kori-thespirit/LoraGatewayDevelopment/code/core/gateway/components/network/eth_w5500_app/include/eth_w5500_app.h

/* -------------------------- LICENSE placeholder -------------------------- */
#ifndef ETH_W5500_APP_H
#define ETH_W5500_APP_H
#include "network_event_group_define.h"
#include "freertos/FreeRTOS.h"
#include "freertos/task.h"
#include "freertos/event_groups.h"
void w5500_init(EventGroupHandle_t *net_eg);
#endif // ETH_W5500_APP_H
