kori-thespirit/LoraGatewayDevelopment/code/unit-test/unit-test_lora_node/components/lora/include/define.h

#ifndef DEFINE_H
#define DEFINE_H

#define CONFIG_CS_GPIO    21
#define CONFIG_MOSI_GPIO  19
#define CONFIG_MISO_GPIO  18
#define CONFIG_SCK_GPIO   4
#define CONFIG_RST_GPIO   22
#define HOST_ID           SPI2_HOST

#endif
