kori-thespirit/LoraGatewayDevelopment/code/unit-test/unit-test_lora_gateway/components/lora/include/define.h

#ifndef DEFINE_H
#define DEFINE_H

#define CONFIG_CS_GPIO    42
#define CONFIG_MOSI_GPIO  41
#define CONFIG_MISO_GPIO  40
#define CONFIG_SCK_GPIO   39
#define CONFIG_RST_GPIO   38
#define HOST_ID           SPI2_HOST

#endif
