kori-thespirit/LoraGatewayDevelopment/code/unit-test/unit-test_w5500_mqtt/main/main.c

#include "esp_err.h"
#include "ethernet_w5500.h"
#include "freertos/FreeRTOS.h"
#include "freertos/queue.h"
#include "freertos/task.h"
#include <stdint.h>

void app_main(void) {
  w5500_init();
  /* Wait until obtain IP address before pinging */
  vTaskDelay(10000 / portTICK_PERIOD_MS);
  ESP_ERROR_CHECK(mqtt_app_start());
  while (1) {
    vTaskDelay(1000 / portTICK_PERIOD_MS);
  }
}
